mbourgeois2/ECE-388-Digital-Level-Design-Project/firmware/atmel projects/final code, may touch up every now and then/accelerometertest/accelerometertest/twi_master.c

/*
* twi_master.c
*
* Created: 09-Jun-19 11:20:17 AM
*  Author: TEP SOVICHEA
*/

#include "twi_master.h"

static ret_code_t tw_start(void)   
{
	/* Send START condition */
#if DEBUG_LOG
	
#endif
	TWCR0 =  (1 << TWINT) | (1 << TWEN) | (1 << TWSTA);
	
	/* Wait for TWINT flag to set */
	while (!(TWCR0 & (1 << TWINT)));
	
	/* Check error */
	if (TWSR0 != TW_START && TWSR0 != TW_REP_START)
	{
#if DEBUG_LOG
		printf("\n");
#endif
		return TWSR0;
	}
	
#if DEBUG_LOG
	printf("SUCCESS\n");
#endif
	return SUCCESS;
}


static void tw_stop(void)
{
	/* Send STOP condition */
#if DEBUG_LOG
	
#endif
	TWCR0 = (1 << TWINT) | (1 << TWEN) | (1 << TWSTO);
}


static ret_code_t tw_write_sla(uint8_t sla)
{
	/* Transmit slave address with read/write flag */
#if DEBUG_LOG
	
#endif
	TWDR0 = sla;
	TWCR0 = (1 << TWINT) | (1 << TWEN);
	
	/* Wait for TWINT flag to set */
	while (!(TWCR0 & (1 << TWINT)));
	if (TWSR0 != TW_MT_SLA_ACK && TWSR0 != TW_MR_SLA_ACK)
	{
#if DEBUG_LOG
		printf("\n");
#endif
		return TWSR0;
	}

#if DEBUG_LOG
	printf("SUCCESS\n");
#endif
	return SUCCESS;
}


static ret_code_t tw_write(uint8_t data)
{
	/* Transmit 1 byte*/
#if DEBUG_LOG
	
#endif
	TWDR0 = data;
	TWCR0 = (1 << TWINT) | (1 << TWEN);
	
	/* Wait for TWINT flag to set */
	while (!(TWCR0 & (1 << TWINT)));
	if (TWSR0 != TW_MT_DATA_ACK)
	{
#if DEBUG_LOG
		printf("\n");
#endif
		return TWSR0;
	}
	
#if DEBUG_LOG
	printf("SUCCESS\n");
#endif
	return SUCCESS;
}


static uint8_t tw_read(bool read_ack)
{
	if (read_ack)
	{
		TWCR0 = (1 << TWINT) | (1 << TWEN) | (1 << TWEA);
		while (!(TWCR0 & (1 << TWINT)));
		if (TWSR0 != TW_MR_DATA_ACK)
		{
			return TWSR0;
		}
	}
	else
	{
		TWCR0 = (1 << TWINT) | (1 << TWEN);
		while (!(TWCR0 & (1 << TWINT)));
		if (TWSR0 != TW_MR_DATA_NACK)
		{
			return TWSR0;
		}
	}
	uint8_t data = TWDR0;
#if DEBUG_LOG
	
#endif
	return data;
}


void tw_init(twi_freq_mode_t twi_freq_mode, bool pullup_en)
{
	DDRC  |= (1 << TW_SDA_PIN) | (1 << TW_SCL_PIN);
	if (pullup_en)
	{
#if DEBUG_LOG
		
#endif
		PORTC |= (1 << TW_SDA_PIN) | (1 << TW_SCL_PIN);
	}
	else
	{
		PORTC &= ~((1 << TW_SDA_PIN) | (1 << TW_SCL_PIN));
	}
	DDRC  &= ~((1 << TW_SDA_PIN) | (1 << TW_SCL_PIN));
	
	switch (twi_freq_mode)
	{
		case TW_FREQ_100K:
		/* Set bit rate register 72 and prescaler to 1 resulting in
		SCL_freq = 16MHz/(16 + 2*72*1) = 100KHz	*/
		TWBR0 = 72;
		break;
		
		case TW_FREQ_250K:
		/* Set bit rate register 24 and prescaler to 1 resulting in
		SCL_freq = 16MHz/(16 + 2*24*1) = 250KHz	*/
		TWBR0 = 24;
		break;
		
		case TW_FREQ_400K:
		/* Set bit rate register 12 and prescaler to 1 resulting in
		SCL_freq = 16MHz/(16 + 2*12*1) = 400KHz	*/
		TWBR0 = 12;
		break;
		
		default: break;
	}
}


ret_code_t tw_master_transmit(uint8_t slave_addr, uint8_t* p_data, uint8_t len, bool repeat_start)
{
	ret_code_t error_code;
	
	/* Send START condition */
	error_code = tw_start();
	if (error_code != SUCCESS)
	{
		return error_code;
	}
	
	/* Send slave address with WRITE flag */
	error_code = tw_write_sla(TW_SLA_W(slave_addr));
	if (error_code != SUCCESS)
	{
		return error_code;
	}
	
	/* Send data byte in single or burst mode */
	for (int i = 0; i < len; ++i)
	{
		error_code = tw_write(p_data[i]);
		if (error_code != SUCCESS)
		{
			return error_code;
		}
	}
	
	if (!repeat_start)
	{
		/* Send STOP condition */
		tw_stop();
	}
	
	return SUCCESS;
}


ret_code_t tw_master_receive(uint8_t slave_addr, uint8_t* p_data, uint8_t len)
{
	ret_code_t error_code;
	
	/* Send START condition */
	error_code = tw_start();
	if (error_code != SUCCESS)
	{
		return error_code;
	}
	
	/* Write slave address with READ flag */
	error_code = tw_write_sla(TW_SLA_R(slave_addr));
	if (error_code != SUCCESS)
	{
		return error_code;
	}
	
	/* Read single or multiple data byte and send ack */
	for (int i = 0; i < len-1; ++i)
	{
		p_data[i] = tw_read(TW_READ_ACK);
	}
	p_data[len-1] = tw_read(TW_READ_NACK);
	
	/* Send STOP condition */
	tw_stop();
	
	return SUCCESS;
}
